Scybin/scyline/3d/switchplate_case.stl

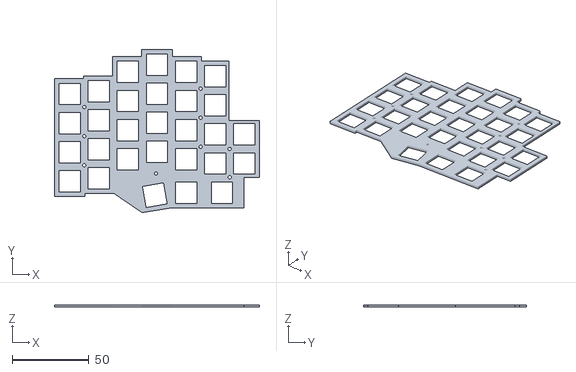
[picture p17: CAD file, 2025-12-28]
3d/switchplate_case.stl
134.0 x 106.7 x 1.60
