Scybin/scyline/ergogen/build/outlines/xlBoard_R.dxf

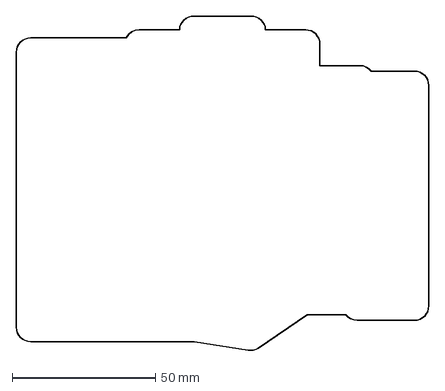
[picture p18: CAD file, 2025-12-28]
ergogen/build/outlines/xlBoard_R.dxf
144.0 x 116.9 mm
