Scybin/scyline/kicad/3d_models/Diode_SOD-123.step

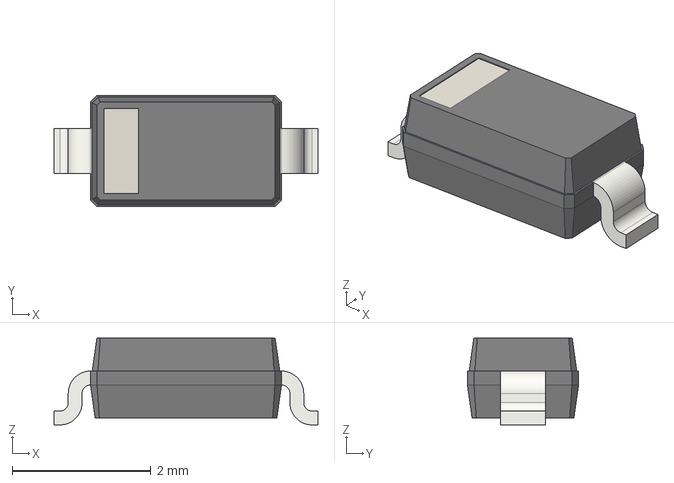
[picture p19: CAD file, 2025-12-18]
kicad/3d_models/Diode_SOD-123.step
3.80 x 1.60 x 1.25 mm
