Scybin/scyline/ergogen/build/outlines/usb_access_R.dxf

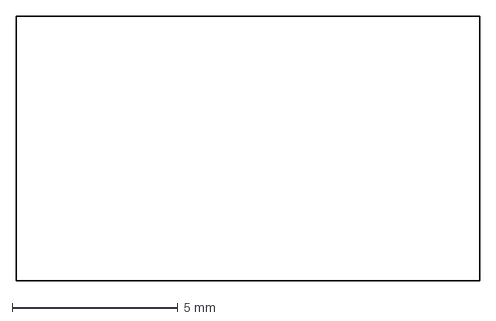
[picture p21: CAD file, 2025-12-28]
ergogen/build/outlines/usb_access_R.dxf
14.0 x 8.00 mm
