Scybin/scyline/kicad/3d_models/MX_1.00u_CAD.step

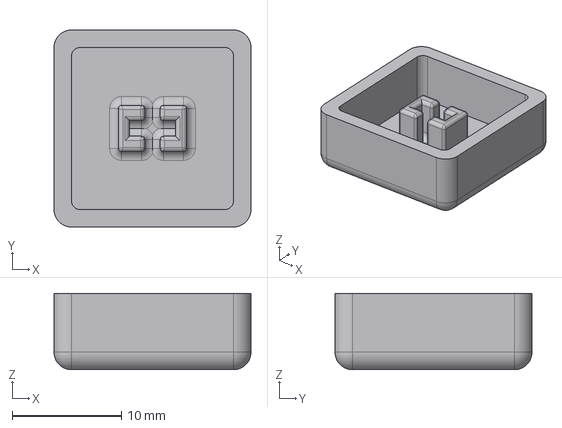
[picture p22: CAD file, 2025-12-18]
kicad/3d_models/MX_1.00u_CAD.step
18.1 x 18.0 x 7.00 mm
