Scybin/scyline/ergogen/build/outlines/wall_insert_L.dxf

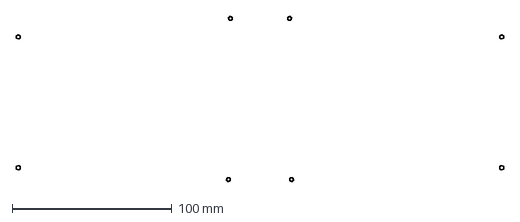
[picture p23: CAD file, 2025-12-28]
ergogen/build/outlines/wall_insert_L.dxf
305.5 x 103.5 mm
