Scybin/scyline/kicad/3d_models/Hotswap_MX.step

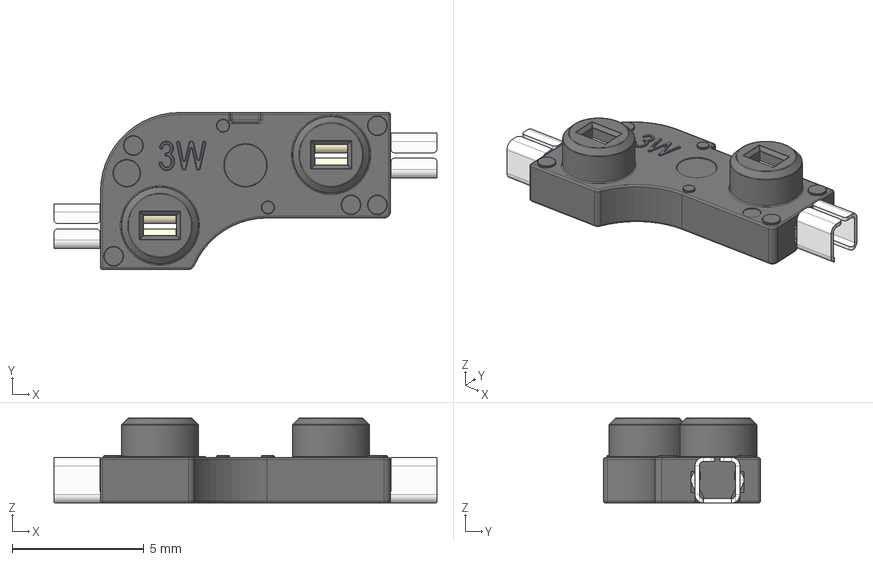
[picture p24: CAD file, 2025-12-18]
kicad/3d_models/Hotswap_MX.step
14.5 x 5.95 x 3.22 mm
