Scybin/scyline/3d/wall_cover_case_tb_L.step

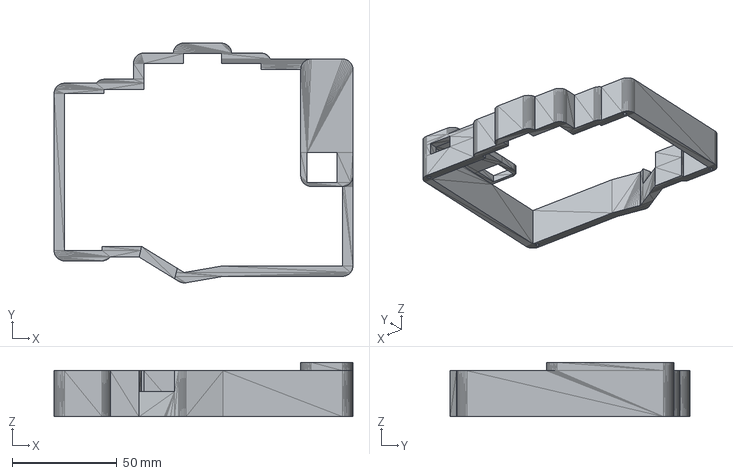
[picture p25: CAD file, 2025-12-25]
3d/wall_cover_case_tb_L.step
143.0 x 114.7 x 26.0 mm
