Scybin/scyline/ergogen/build/outlines/usb_wall_R.dxf

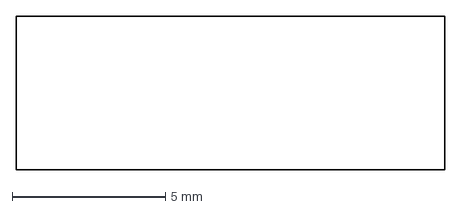
[picture p26: CAD file, 2025-12-28]
ergogen/build/outlines/usb_wall_R.dxf
14.0 x 5.00 mm
