Scybin/scyline/kicad/3d_models/MX_CAD.step

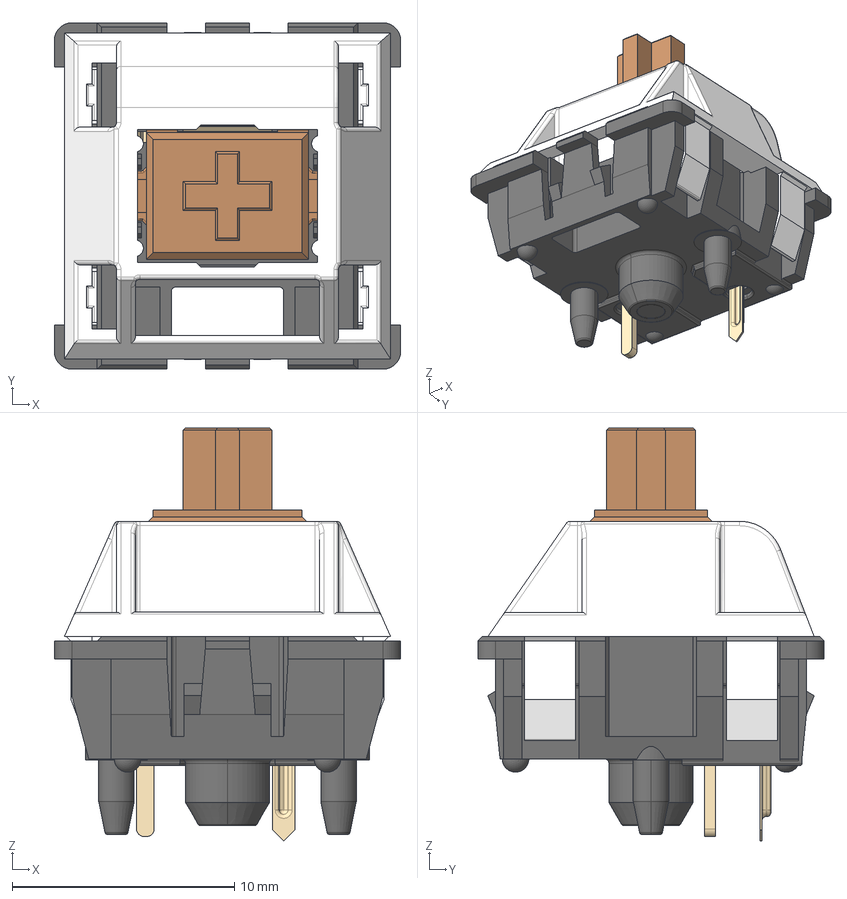
[picture p27: CAD file, 2025-12-18]
kicad/3d_models/MX_CAD.step
15.6 x 15.6 x 18.6 mm
