Scybin/scyline/3d/case.step

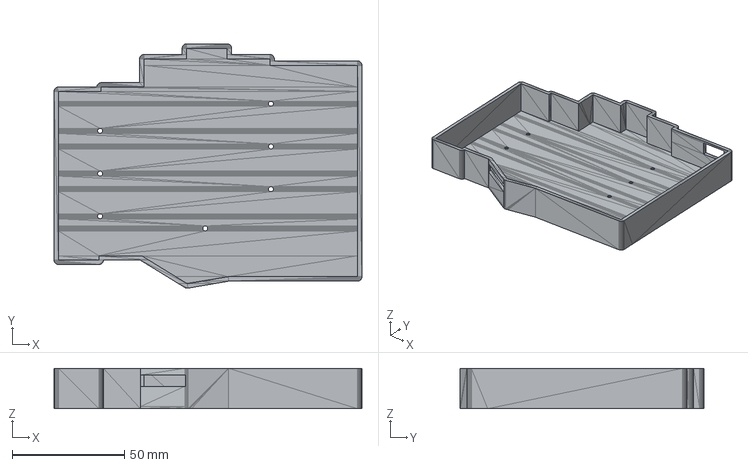
[picture p28: CAD file, 2025-12-20]
3d/case.step
137.0 x 108.7 x 18.0 mm
