Scybin/scyline/ergogen/build/outlines/button_wall_R.dxf

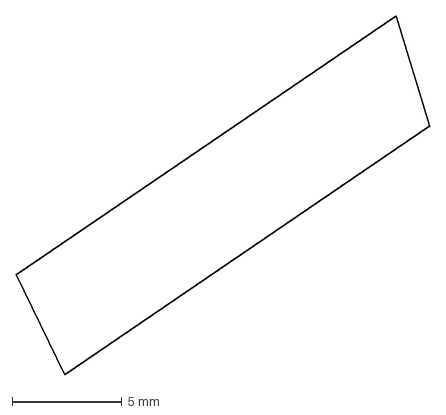
[picture p29: CAD file, 2025-12-28]
ergogen/build/outlines/button_wall_R.dxf
18.9 x 16.3 mm
