Scybin/scyline/kicad/3d_models/Switch_MSK12C02.step

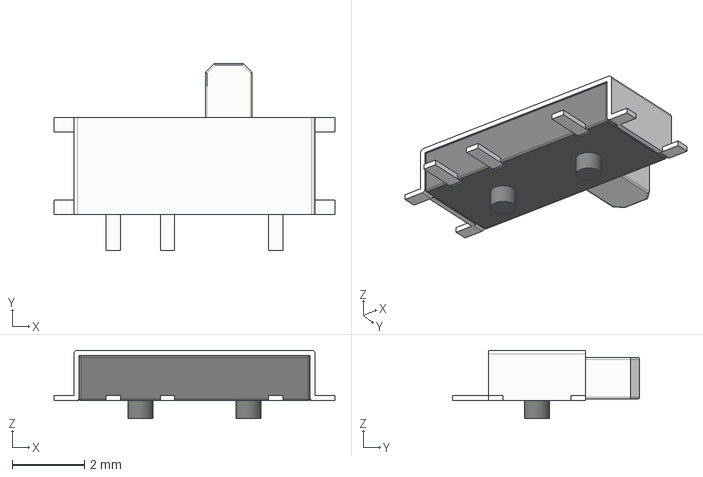
[picture p30: CAD file, 2025-12-18]
kicad/3d_models/Switch_MSK12C02.step
7.80 x 5.20 x 1.90 mm
