Scybin/scyline/ergogen/build/outlines/insert.dxf

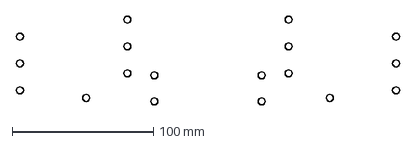
[picture p31: CAD file, 2025-12-28]
ergogen/build/outlines/insert.dxf
271.0 x 62.9 mm
