Scybin/scyline/kicad/3d_models/Nice_Nano_V2_Flipped.step

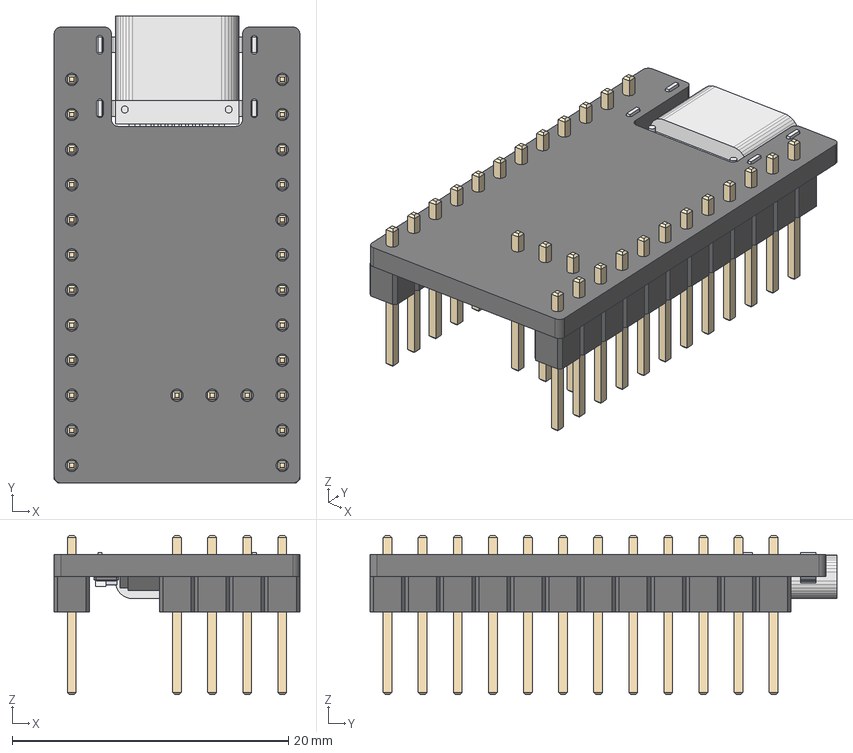
[picture p32: CAD file, 2025-12-18]
kicad/3d_models/Nice_Nano_V2_Flipped.step
17.8 x 33.8 x 11.5 mm
PinHeader_1x12_P2.54mm_Vertical.step
User Library-TYPE-C-31-M-14.step
MICRO_603 resistor 102
MICRO_stackable header pin x 12
MICRO_stackable header 12
micro_crystal 5x3
MICRO_led
micro_MIC5219
