Scybin/scyline/ergogen/build/outlines/cover_tb_se_corner_R.dxf

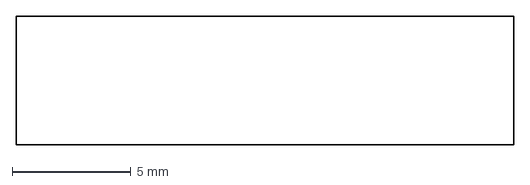
[picture p33: CAD file, 2025-12-28]
ergogen/build/outlines/cover_tb_se_corner_R.dxf
21.0 x 5.40 mm
