Scybin/scyline/kicad/3d_models/MX_1.50u_CAD.step

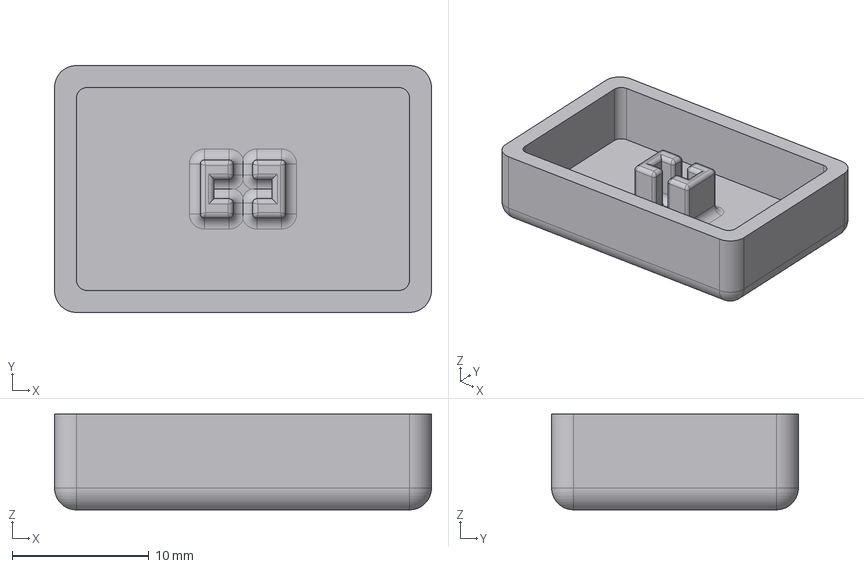
[picture p34: CAD file, 2025-12-18]
kicad/3d_models/MX_1.50u_CAD.step
27.6 x 18.1 x 7.00 mm
