Scybin/scyline/ergogen/build/outlines/cover_R.dxf

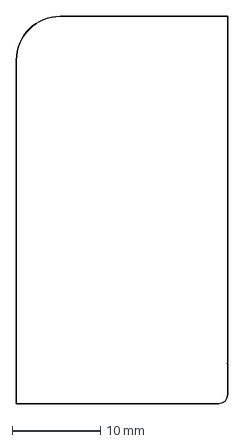
[picture p35: CAD file, 2025-12-28]
ergogen/build/outlines/cover_R.dxf
24.0 x 44.0 mm
