Scybin/scyline/ergogen/build/outlines/cover_se_corner_R.dxf

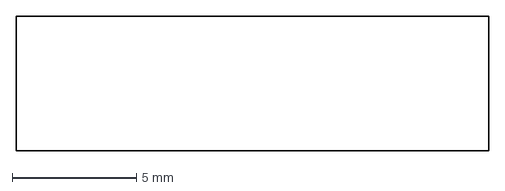
[picture p37: CAD file, 2025-12-28]
ergogen/build/outlines/cover_se_corner_R.dxf
19.0 x 5.40 mm
