Scybin/scyline/ergogen/build/outlines/cover_nw_corner_R.dxf

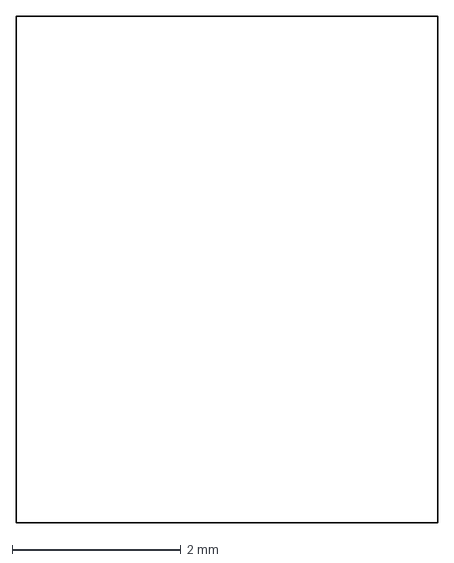
[picture p38: CAD file, 2025-12-28]
ergogen/build/outlines/cover_nw_corner_R.dxf
5.00 x 6.00 mm
