Scybin/scyline/ergogen/build/outlines/plate_hole.dxf

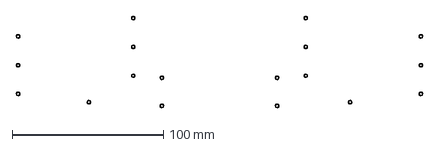
[picture p39: CAD file, 2025-12-28]
ergogen/build/outlines/plate_hole.dxf
268.2 x 60.1 mm
