Scybin/scyline/ergogen/build/outlines/switch_cutout.dxf

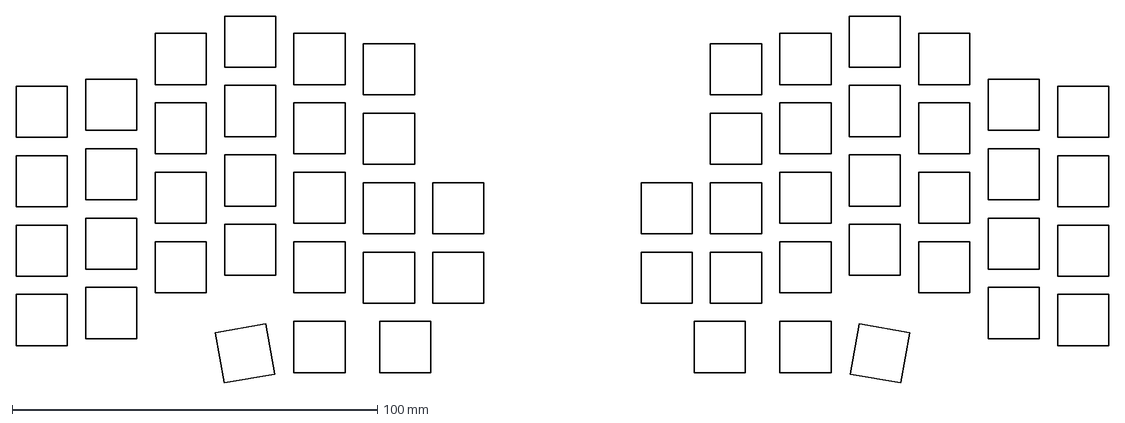
[picture p40: CAD file, 2025-12-28]
ergogen/build/outlines/switch_cutout.dxf
299.0 x 100.4 mm
