Scybin/scyline/ergogen/build/outlines/pcb_R.dxf

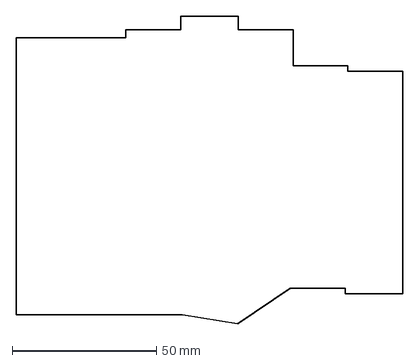
[picture p41: CAD file, 2025-12-28]
ergogen/build/outlines/pcb_R.dxf
134.0 x 106.7 mm
