Scybin/scyline/ergogen/build/outlines/cover_tb_cut_R.dxf

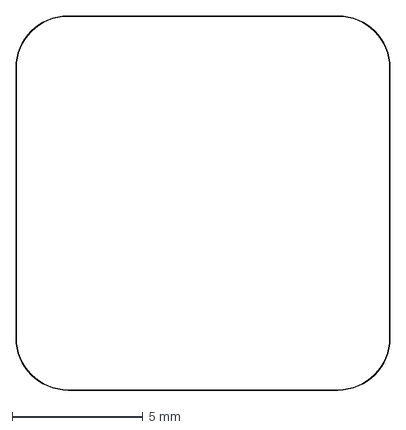
[picture p42: CAD file, 2025-12-28]
ergogen/build/outlines/cover_tb_cut_R.dxf
14.3 x 14.3 mm
