Scybin/scyline/ergogen/build/outlines/cover_tb_R.dxf

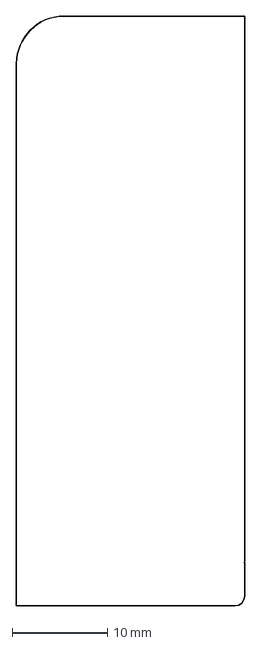
[picture p43: CAD file, 2025-12-28]
ergogen/build/outlines/cover_tb_R.dxf
24.0 x 62.0 mm
