Scybin/scyline/ergogen/build/outlines/button_access_R.dxf

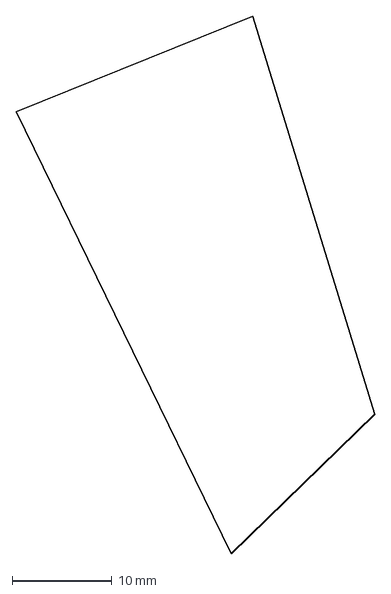
[picture p44: CAD file, 2025-12-28]
ergogen/build/outlines/button_access_R.dxf
36.1 x 54.0 mm
