Scybin/scyline/ergogen/build/outlines/trackball_wall_access_R.dxf

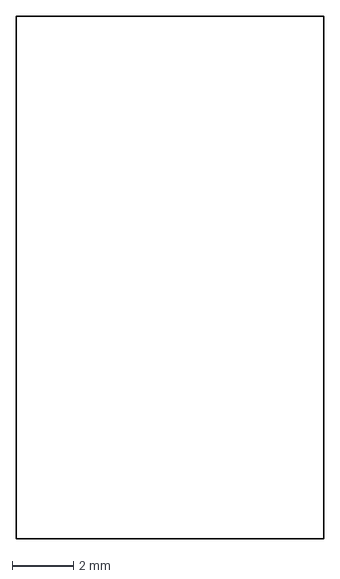
[picture p45: CAD file, 2025-12-28]
ergogen/build/outlines/trackball_wall_access_R.dxf
10.0 x 17.0 mm
