Scybin/scyline/ergogen/build/outlines/switch_cutout_test.dxf

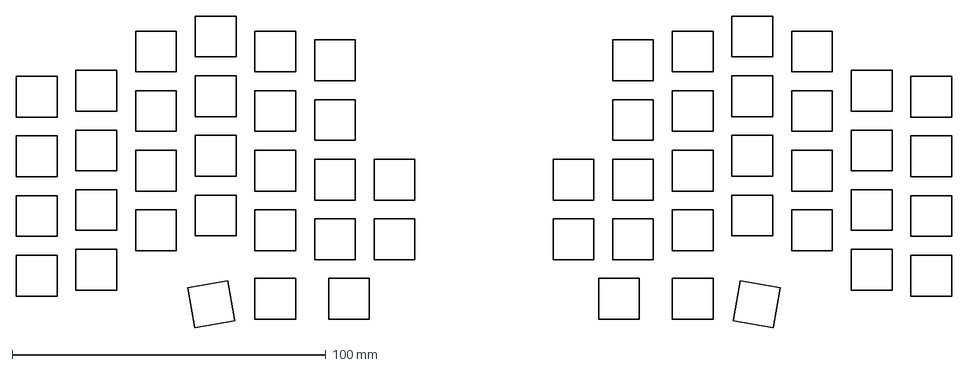
[picture p47: CAD file, 2025-12-28]
ergogen/build/outlines/switch_cutout_test.dxf
298.0 x 99.3 mm
