Scybin/scyline/ergogen/build/outlines/keycap_outline.dxf

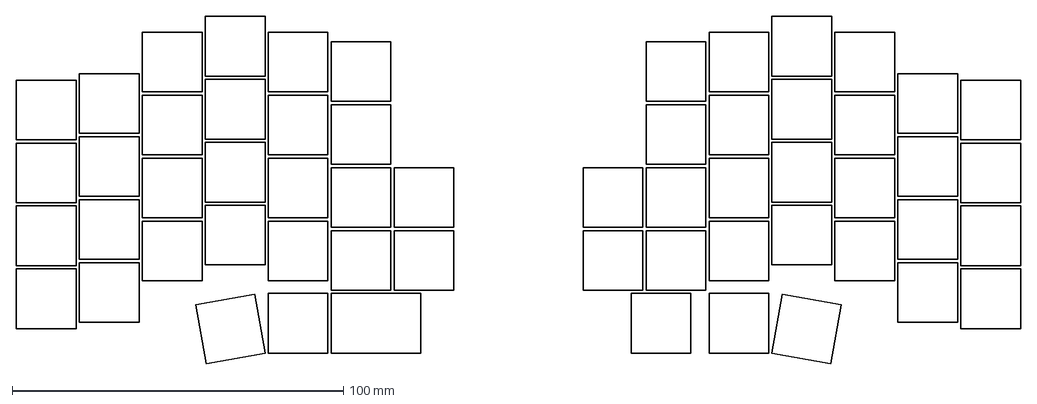
[picture p48: CAD file, 2025-12-28]
ergogen/build/outlines/keycap_outline.dxf
303.0 x 104.7 mm
