Scybin/scyline/ergogen/build/outlines/cover_sw_corner_R.dxf

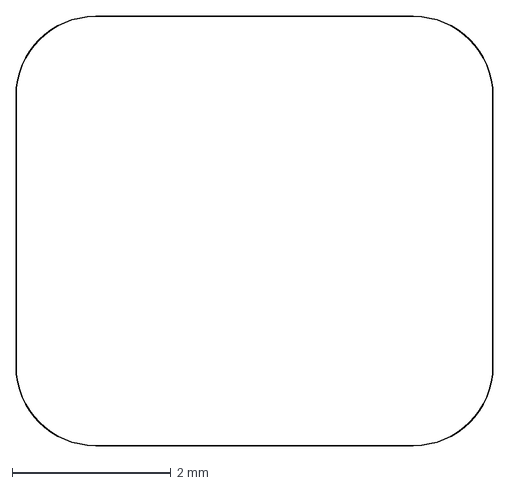
[picture p49: CAD file, 2025-12-28]
ergogen/build/outlines/cover_sw_corner_R.dxf
6.00 x 5.40 mm
