Scybin/scyline/ergogen/build/outlines/cover_tb_sw_corner_R.dxf

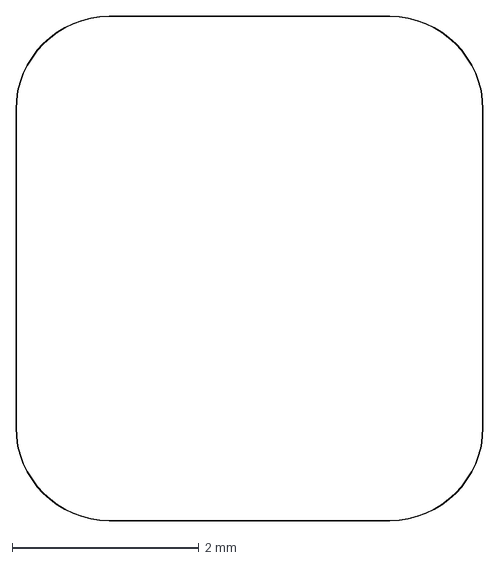
[picture p50: CAD file, 2025-12-28]
ergogen/build/outlines/cover_tb_sw_corner_R.dxf
5.00 x 5.40 mm
