Scybin/scyline/ergogen/build/outlines/trackball_wall_R.dxf

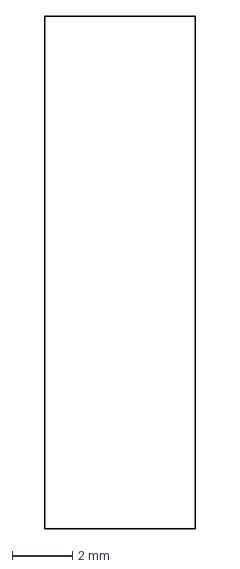
[picture p51: CAD file, 2025-12-28]
ergogen/build/outlines/trackball_wall_R.dxf
5.00 x 17.0 mm
