Scybin/scyline/ergogen/build/outlines/cover_nw_corner_L.dxf

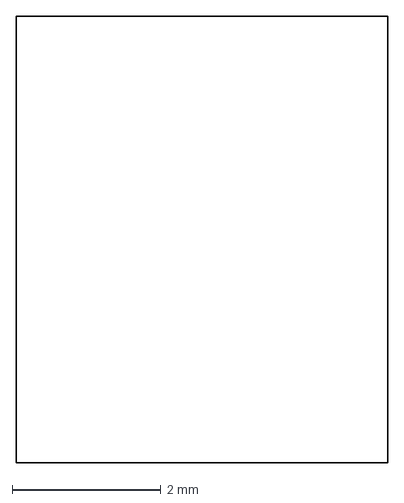
[picture p52: CAD file, 2025-12-26]
ergogen/build/outlines/cover_nw_corner_L.dxf
5.00 x 6.00 mm
