Scybin/scyline/ergogen/build/outlines/cover_tb_L.dxf

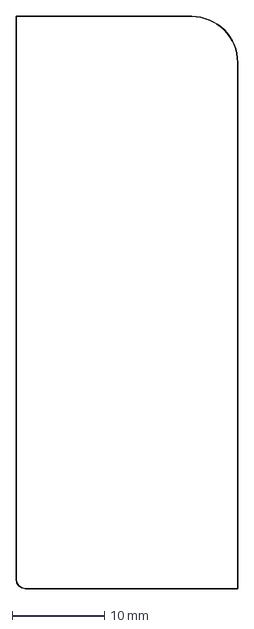
[picture p53: CAD file, 2025-12-26]
ergogen/build/outlines/cover_tb_L.dxf
24.0 x 62.0 mm
