Scybin/scyline/ergogen/build/outlines/cover_se_corner_L.dxf

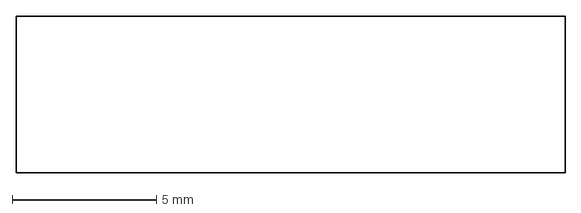
[picture p54: CAD file, 2025-12-26]
ergogen/build/outlines/cover_se_corner_L.dxf
19.0 x 5.40 mm
