Scybin/scyline/ergogen/build/outlines/cover_L.dxf

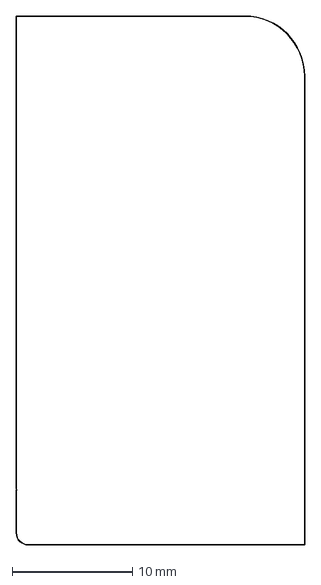
[picture p55: CAD file, 2025-12-26]
ergogen/build/outlines/cover_L.dxf
24.0 x 44.0 mm
