Scybin/scyline/ergogen/build/outlines/cover_sw_corner_L.dxf

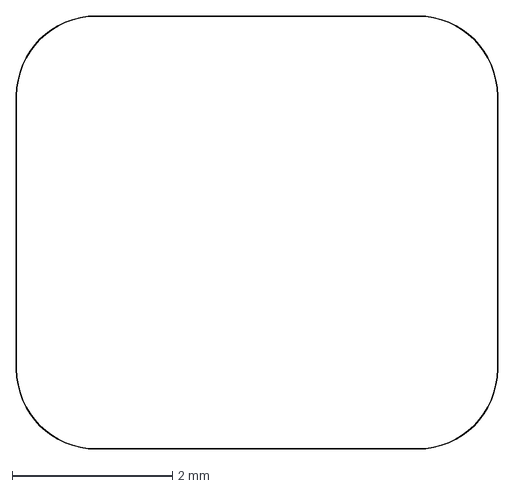
[picture p56: CAD file, 2025-12-26]
ergogen/build/outlines/cover_sw_corner_L.dxf
6.00 x 5.40 mm
