Scybin/scyline/ergogen/build/outlines/inner_lip_L.dxf

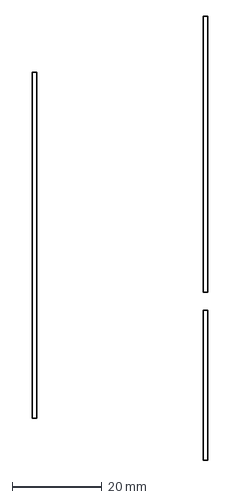
[picture p57: CAD file, 2025-12-26]
ergogen/build/outlines/inner_lip_L.dxf
39.0 x 98.8 mm
