Scybin/scyline/ergogen/build/outlines/bottom_lip_rect_L.dxf

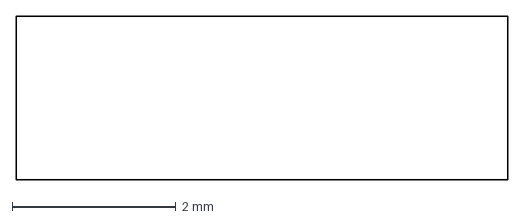
[picture p58: CAD file, 2025-12-26]
ergogen/build/outlines/bottom_lip_rect_L.dxf
6.00 x 2.00 mm
