Scybin/scyline/ergogen/build/outlines/bottom_lip_cut_L.dxf

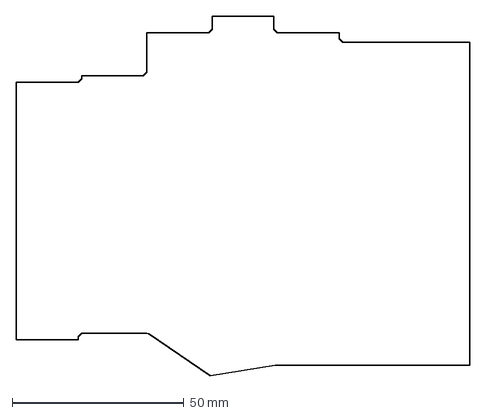
[picture p59: CAD file, 2025-12-26]
ergogen/build/outlines/bottom_lip_cut_L.dxf
132.0 x 104.7 mm
