Scybin/scyline/ergogen/build/outlines/button_access_L.dxf

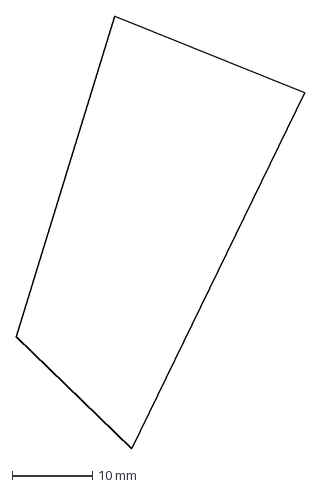
[picture p60: CAD file, 2025-12-26]
ergogen/build/outlines/button_access_L.dxf
36.1 x 54.0 mm
