Scybin/scyline/ergogen/build/outlines/cover_tb_sw_corner_L.dxf

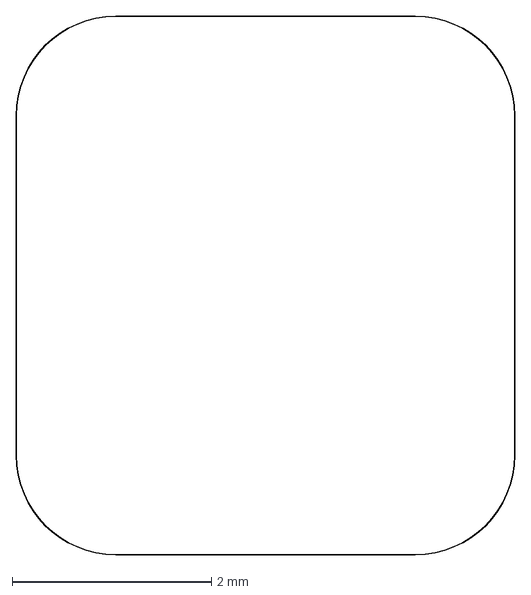
[picture p61: CAD file, 2025-12-26]
ergogen/build/outlines/cover_tb_sw_corner_L.dxf
5.00 x 5.40 mm
