Scybin/scyline/ergogen/build/outlines/usb_wall_L.dxf

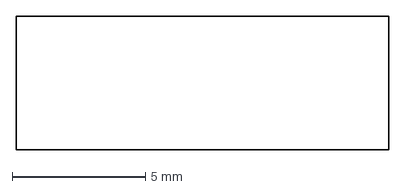
[picture p62: CAD file, 2025-12-26]
ergogen/build/outlines/usb_wall_L.dxf
14.0 x 5.00 mm
