Scybin/scyline/ergogen/build/outlines/usb_access_L.dxf

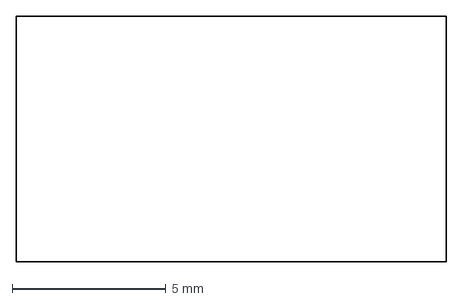
[picture p63: CAD file, 2025-12-26]
ergogen/build/outlines/usb_access_L.dxf
14.0 x 8.00 mm
