Scybin/scyline/ergogen/build/outlines/switchplate_tb.dxf

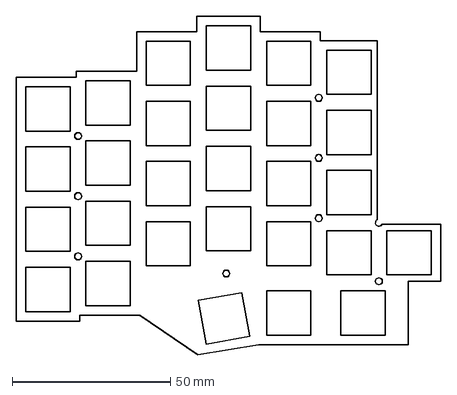
[picture p64: CAD file, 2025-12-26]
ergogen/build/outlines/switchplate_tb.dxf
134.0 x 106.7 mm
