Scybin/scyline/ergogen/build/outlines/cover_tb_se_corner_L.dxf

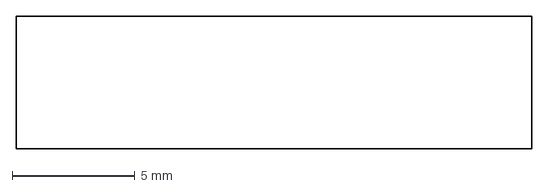
[picture p65: CAD file, 2025-12-26]
ergogen/build/outlines/cover_tb_se_corner_L.dxf
21.0 x 5.40 mm
