Scybin/scyline/ergogen/build/outlines/button_wall_L.dxf

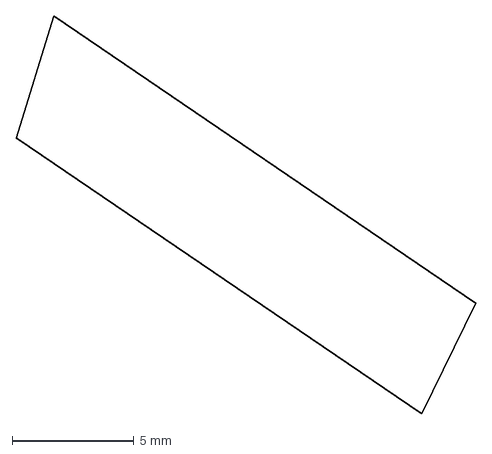
[picture p66: CAD file, 2025-12-26]
ergogen/build/outlines/button_wall_L.dxf
18.9 x 16.3 mm
