Scybin/scyline/ergogen/build/outlines/switchplate.dxf

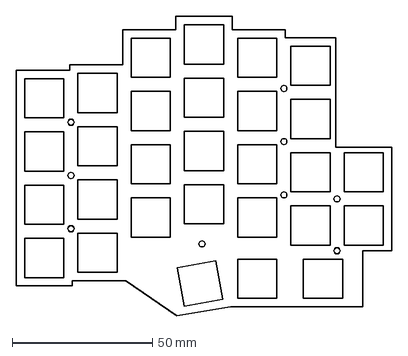
[picture p67: CAD file, 2025-12-26]
ergogen/build/outlines/switchplate.dxf
134.0 x 106.7 mm
