Scybin/scyline/ergogen/build/outlines/mcu_lip_clear_L.dxf

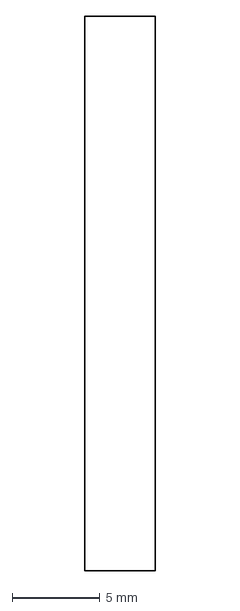
[picture p68: CAD file, 2025-12-26]
ergogen/build/outlines/mcu_lip_clear_L.dxf
4.00 x 31.6 mm
