Scybin/scyline/ergogen/build/outlines/xlBoard_L.dxf

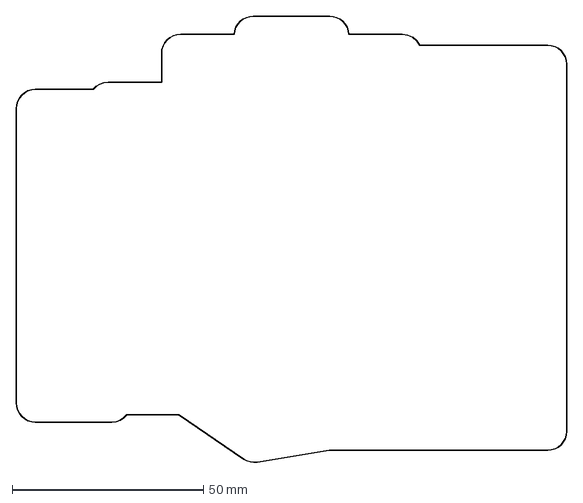
[picture p69: CAD file, 2025-12-26]
ergogen/build/outlines/xlBoard_L.dxf
144.0 x 116.9 mm
