Scybin/scyline/ergogen/build/outlines/pcb_L.dxf

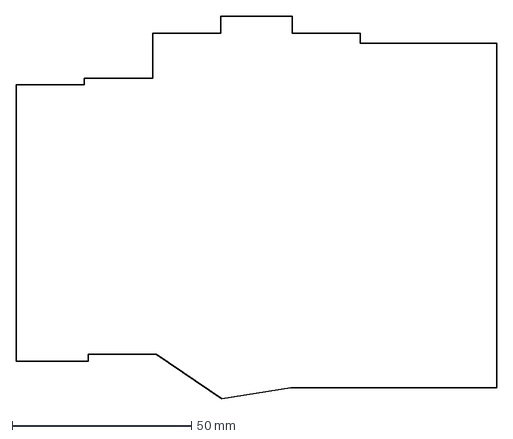
[picture p70: CAD file, 2025-12-26]
ergogen/build/outlines/pcb_L.dxf
134.0 x 106.7 mm
