Scybin/scyline/ergogen/build/outlines/pcb_notch_circle_L.dxf

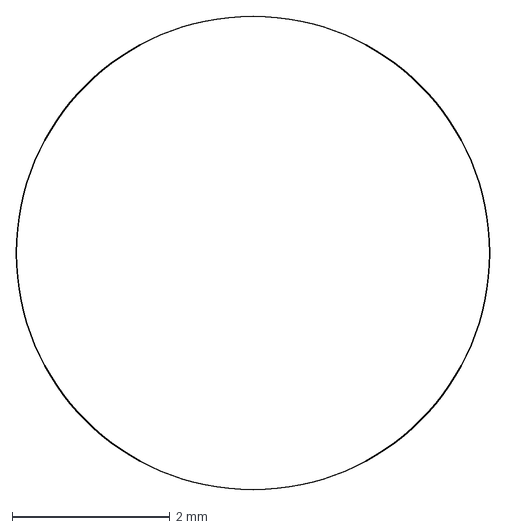
[picture p71: CAD file, 2025-12-26]
ergogen/build/outlines/pcb_notch_circle_L.dxf
6.00 x 6.00 mm
