Scybin/scyline/ergogen/build/outlines/pcb_notched_L.dxf

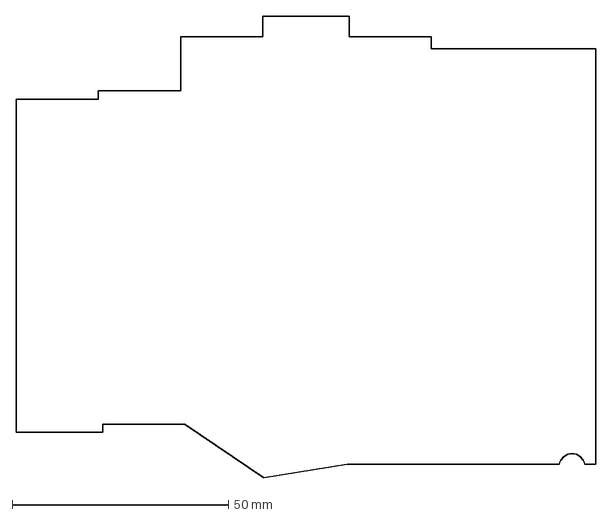
[picture p72: CAD file, 2025-12-26]
ergogen/build/outlines/pcb_notched_L.dxf
134.0 x 106.7 mm
