Scybin/scyline/ergogen/build/outlines/wall_clearance.dxf

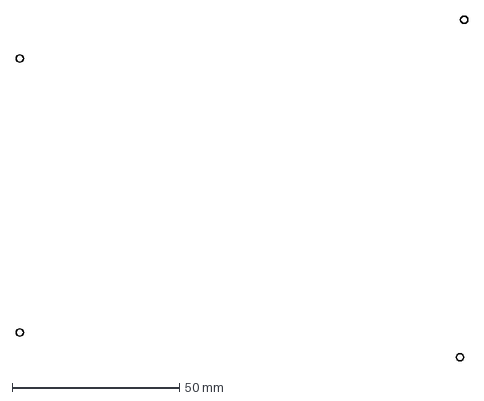
[picture p74: CAD file, 2025-12-26]
ergogen/build/outlines/wall_clearance.dxf
135.2 x 103.2 mm
