Scybin/scyline/ergogen/build/outlines/trackball_wall_L.dxf

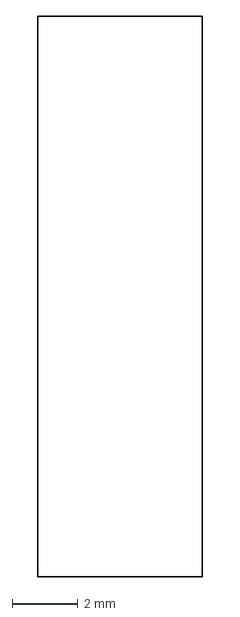
[picture p75: CAD file, 2025-12-25]
ergogen/build/outlines/trackball_wall_L.dxf
5.00 x 17.0 mm
