Scybin/scyline/ergogen/build/outlines/trackball_wall_access_L.dxf

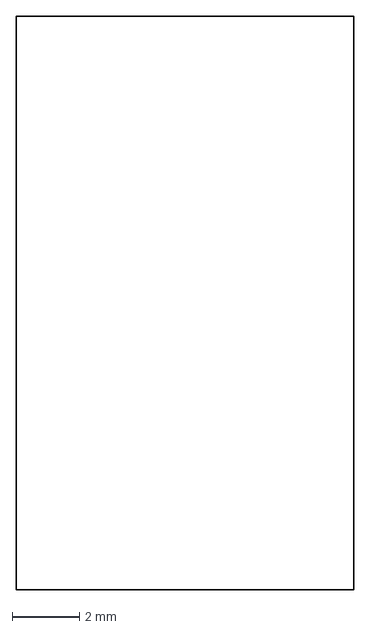
[picture p76: CAD file, 2025-12-25]
ergogen/build/outlines/trackball_wall_access_L.dxf
10.0 x 17.0 mm
