Scybin/scyline/ergogen/build/outlines/cover_tb_cut_L.dxf

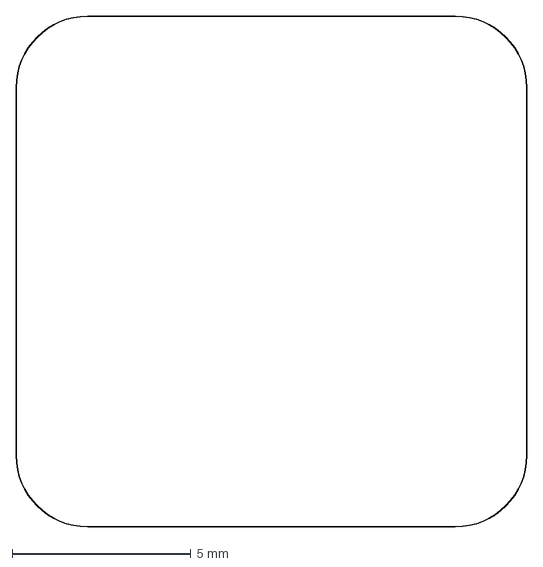
[picture p77: CAD file, 2025-12-25]
ergogen/build/outlines/cover_tb_cut_L.dxf
14.3 x 14.3 mm
